devjonix/arena9/parts-middle/arena_holder_lower.stl

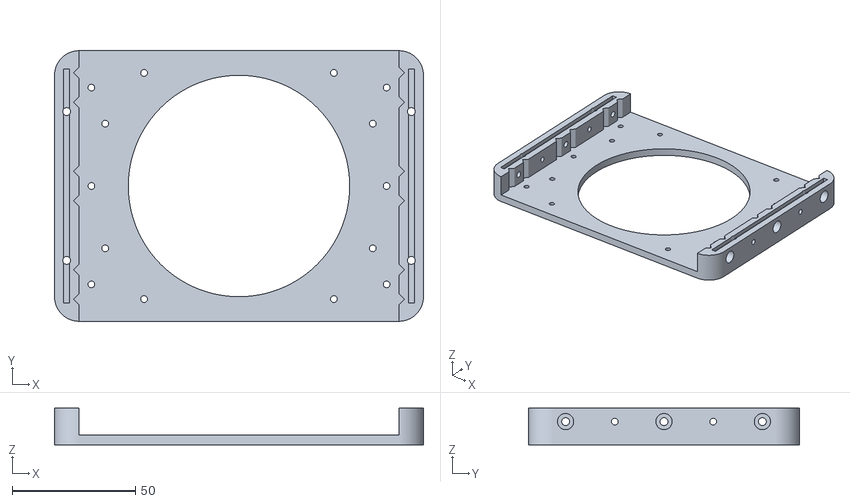
[picture p18: CAD file, 2024-07-03]
parts-middle/arena_holder_lower.stl
150.0 x 110.0 x 15.0
