devjonix/arena9/parts-bottom/sholder/bottom_screenholder_feetB.stl

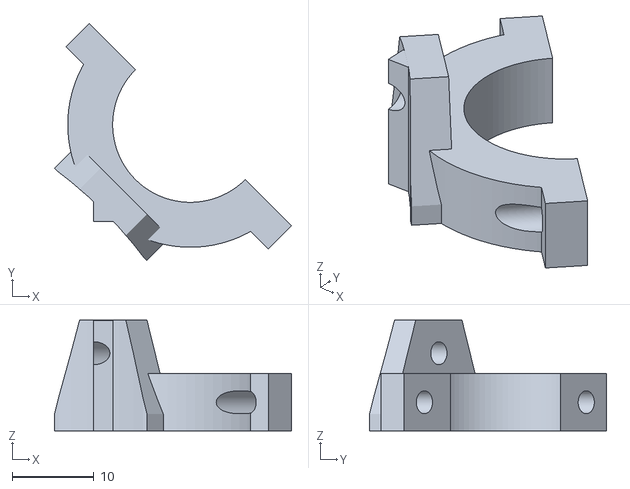
[picture p19: CAD file, 2024-07-22]
parts-bottom/sholder/bottom_screenholder_feetB.stl
29.0 x 29.0 x 13.5
