devjonix/arena9/parts-middle/contactor.stl

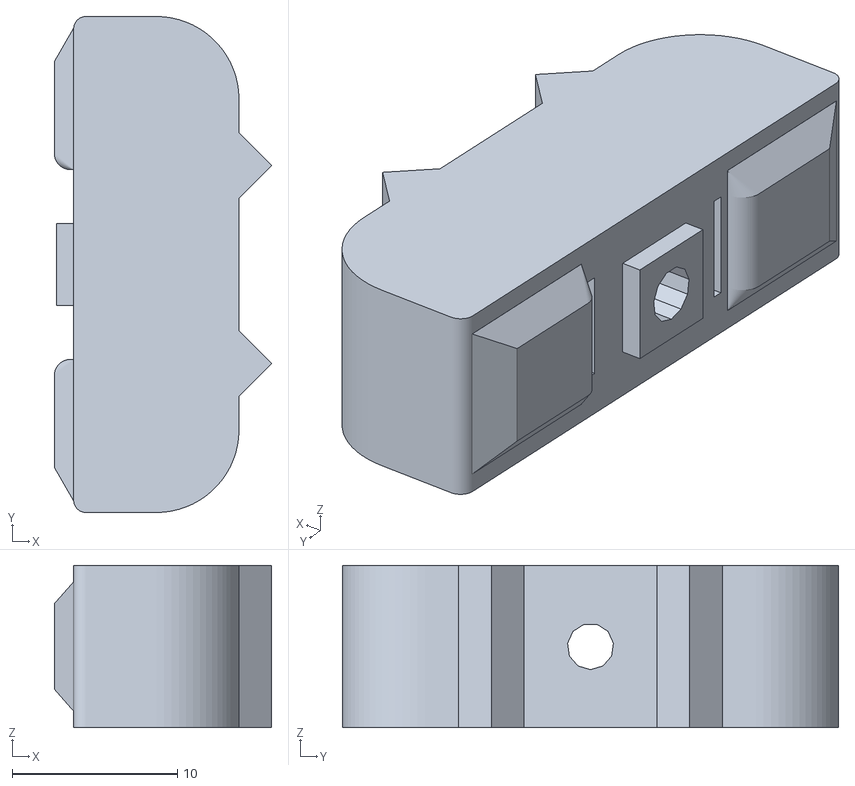
[picture p20: CAD file, 2024-07-03]
parts-middle/contactor.stl
13.2 x 30.0 x 9.80
