devjonix/arena9/parts-top/top_top-ring.stl

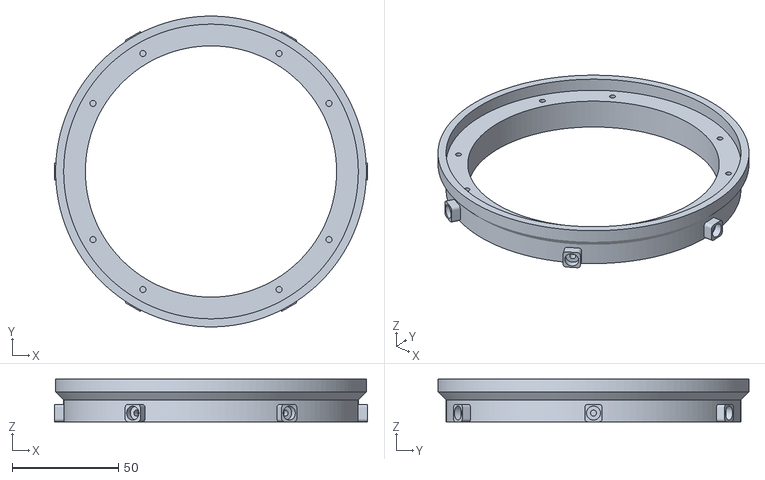
[picture p21: CAD file, 2024-07-03]
parts-top/top_top-ring.stl
147.0 x 146.0 x 20.0
