devjonix/arena9/parts-middle/contactor_v2.stl

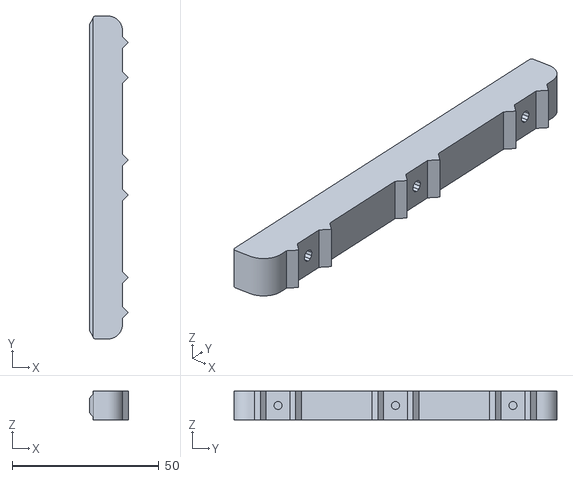
[picture p22: CAD file, 2024-07-03]
parts-middle/contactor_v2.stl
13.2 x 110.0 x 9.80
