devjonix/arena9/parts-top/top_tube_8cm.stl

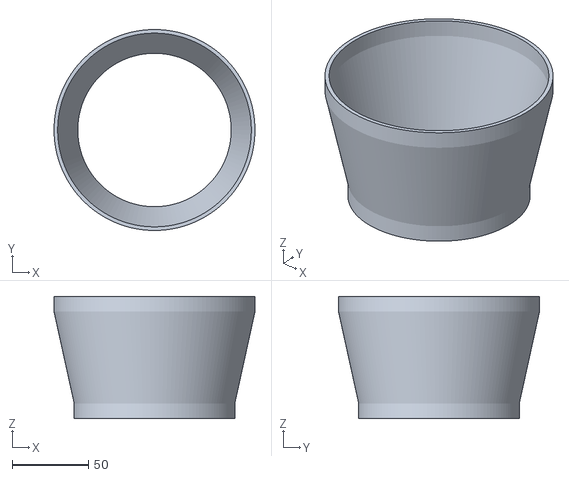
[picture p23: CAD file, 2024-07-03]
parts-top/top_tube_8cm.stl
131.8 x 131.8 x 80.0
