devjonix/arena9/parts-middle/arena_holder_upper.stl

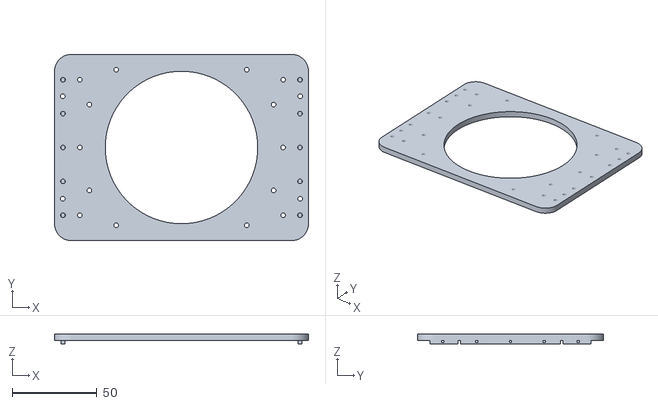
[picture p24: CAD file, 2024-07-03]
parts-middle/arena_holder_upper.stl
150.0 x 110.0 x 6.01
