devjonix/arena9/parts-top/top_tube_12cm.stl

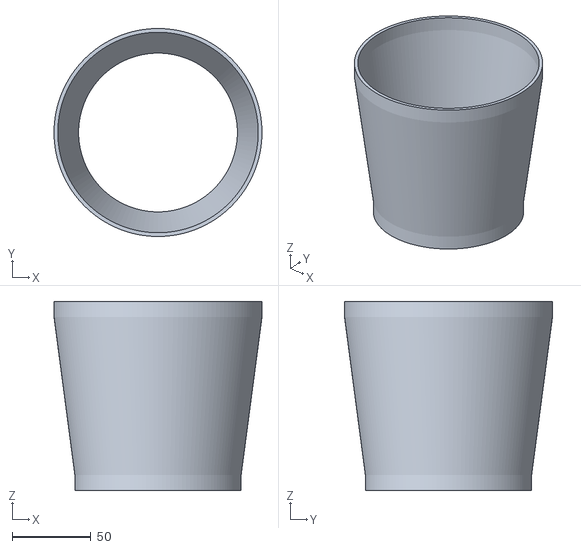
[picture p25: CAD file, 2024-07-03]
parts-top/top_tube_12cm.stl
131.8 x 131.8 x 120.0
