devjonix/arena9/parts-middle/arena_holder_upper_with-extra-tol.stl

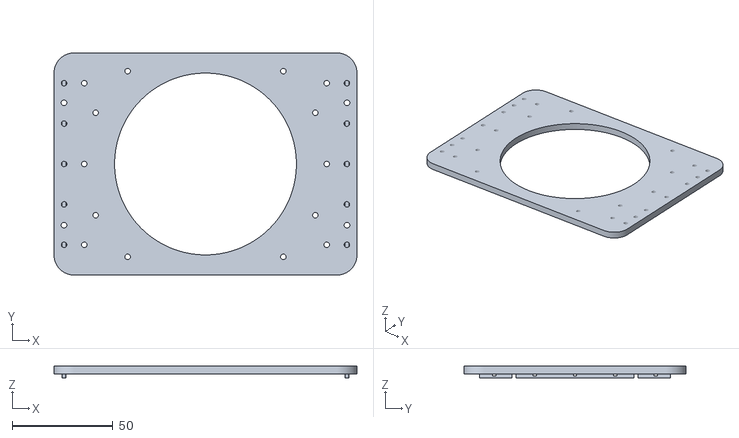
[picture p26: CAD file, 2024-07-03]
parts-middle/arena_holder_upper_with-extra-tol.stl
150.0 x 110.0 x 5.91
