devjonix/arena9/parts-top/top_plate.stl

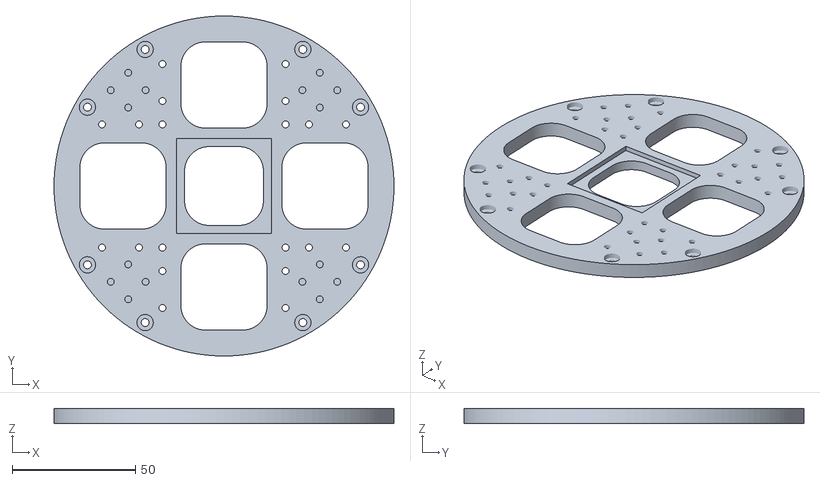
[picture p27: CAD file, 2024-07-03]
parts-top/top_plate.stl
138.0 x 138.0 x 6.00
