devjonix/arena9/parts-top/top_plate-camplate.stl

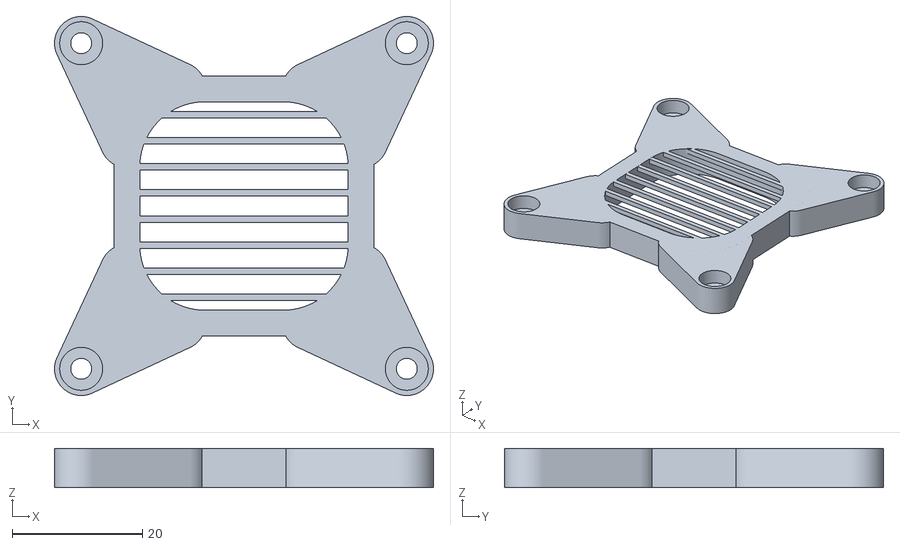
[picture p28: CAD file, 2024-07-03]
parts-top/top_plate-camplate.stl
58.2 x 58.2 x 6.01
