devjonix/arena9/parts-top/top_plate-ledholder-cairn.stl

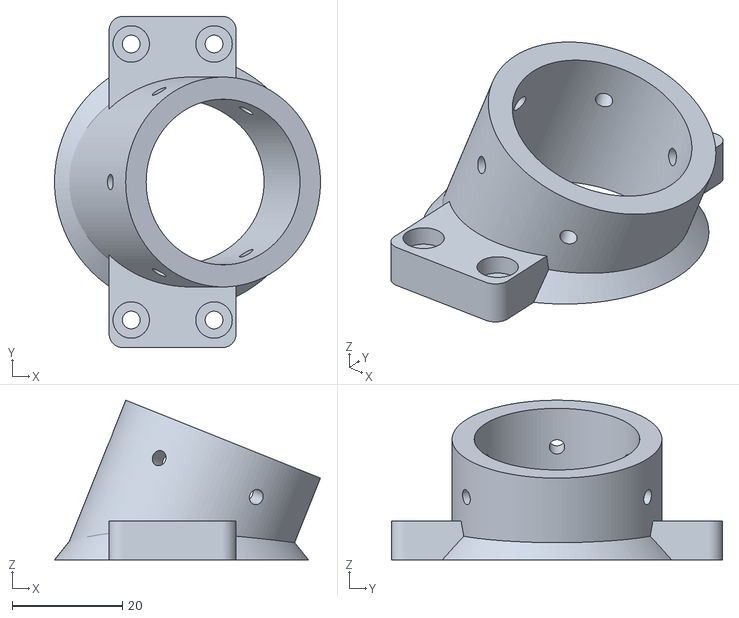
[picture p29: CAD file, 2024-07-03]
parts-top/top_plate-ledholder-cairn.stl
48.2 x 60.0 x 28.9
